OSHE-Github/Class-H-Amplifier/LTspice Simulation Files/Rail_Splitter_Sim.asc

C1: cap; 1n
C2: cap; 10µ
C3: cap; 100n
C4: cap; 30µ
C5: cap; 30µ
C6: cap; 47µ
C7: cap; 47µ
C8: cap; 1m
C9: cap; 1m
C10: cap; 4.7n
C11: cap; 2.2n
C12: cap; 10µ
D2: diode
D3: diode
L1: ind; 5µ
L2: ind; 22µ
L3: ind; 12µ
R1: res; 0.75
R2: res; 5k
R3: res; 12k
R4: res; 0.75
R7: res; 330
R8: res; 5k
R9: res; 3.9k
R10: res; 3.3k
R11: res; 12k
R12: res; 4.7k
R13: res; 82k
R14: res; 33k
R15: res; 5.6k
U2: SQJA80EP
U3: SQJA80EP
U4: AD820
U5: IRS21531DS
V1: voltage; 12; Rser=1
V2: voltage; 20
Named nets: 0, com, VCC, Control, V+
.options reltol=0.01 abstol=1e-8 method=gear
.options itl4=500 itl6=200
.tran 0 200m 0 0.5u uic
