OSHE-Github/Class-H-Amplifier/LTspice Simulation Files/AB_Amplifier.asc

C1: cap; 0.1µ
C2: cap; 0.1µ
C3: cap; 1n
C4: cap; 30p
Q1: npn; 2N5551C
Q2: npn; MJE15032C
Q3: npn; MJL21194C
Q4: pnp; MJL21193C
Q5: pnp; MJE15033C
Q6: npn; MJE15032C
Q7: pnp; MJE15033C
Q8: pnp; 2N5401C
Q9: pnp; 2N5401C
Q10: npn; 2N5551C
Q11: npn; 2N5551C
R1: res; 1k
R2: res; 20k
R3: res; 1k
R4: res; 108
R5: res; 3.6k
R6: res; 1.1k
R7: res; 100
R8: res; 1
R9: res; 8
R10: res; 1
R11: res; 40k
R12: res; 108
R13: res; 40k
R14: res; 330
U1: OPA454
U2: pot; Rtot=1K wiper=.2
V1: voltage; -45
V2: voltage; 45
V3: voltage; SINE(0 1 1k)
Named nets: 0, V-, V+, Out, Vout
.include "Cordell Models.txt"
.op
THD - select view FFT on plot to view and look at error log for THD %
.tran 0 4ms 0 0.488u
.option plotwinsize=0
.options reltol=0.01 abstol=1e-6 vntol=1e-4
.four 1kHz 10 4 V(vout)
Frequency Response, change V3 to be AC 1 instead of SINE
.ac dec 10 20 1Meg
DC Operating Point
Transient Response: Alt Click on RL to see power, CTRL+Click on trace name 
to see RMS. Max at 1.9V amplitude
.noise V(Vout) V3 dec 20 20 20k
.include pot.sub
